pratipo/kiwo/kiwoAlpha_soft/kiwoParser.h

#pragma once

#include "JsonListener.h"

class kiwoParser: public JsonListener {

  public:
    virtual void whitespace(char c);
  
    virtual void startDocument();

    virtual void key(String key);

    virtual void value(String value);

    virtual void endArray();

    virtual void endObject();

    virtual void endDocument();

    virtual void startArray();

    virtual void startObject();
};
